PedroContipelli/Autonomous-Guitar/ESP32/boot.py

try:
    import usocket as socket
except:
    import socket
    
from machine import Pin
import network
import ESP32.front_end
import esp
esp.osdebug(None)

import gc
gc.collect()

ssid = '**********'
password = '************'

station = network.WLAN(network.STA_IF)

station.active(True)
station.connect(ssid, password)

while station.isconnected() == False:
    pass

print('Connection successful')
print(station.ifconfig())
ESP32.front_end.main()
